ElectronicCats/RS485_Modbus_FeatherWing/Fw/Examples/ModbusRTUServerKitchenSink/ModbusRTUServerKitchenSink.ino

/*
Modbus example

  Andres Sabas @ Electronic Cats
  Original Creation Date: May 27, 2021
  Development environment specifics:

  This code is beerware; if you see me (or any other Electronic Cats
  member) at the local, and you've found our code helpful,
  please buy us a round!
  Distributed as-is; no warranty is given.
*/

#include <ArduinoRS485.h> // ArduinoModbus depends on the ArduinoRS485 library
#include <ArduinoModbus.h>

const int numCoils = 10;
const int numDiscreteInputs = 10;
const int numHoldingRegisters = 10;
const int numInputRegisters = 10;

void setup() {
  Serial.begin(9600);
  while (!Serial);

  Serial.println("Modbus RTU Server Kitchen Sink");

  // start the Modbus RTU server, with (slave) id 42
  if (!ModbusRTUServer.begin(42, 9600)) {
    Serial.println("Failed to start Modbus RTU Server!");
    while (1);
  }

  // configure coils at address 0x00
  ModbusRTUServer.configureCoils(0x00, numCoils);

  // configure discrete inputs at address 0x00
  ModbusRTUServer.configureDiscreteInputs(0x00, numDiscreteInputs);

  // configure holding registers at address 0x00
  ModbusRTUServer.configureHoldingRegisters(0x00, numHoldingRegisters);

  // configure input registers at address 0x00
  ModbusRTUServer.configureInputRegisters(0x00, numInputRegisters);
}

void loop() {
  // poll for Modbus RTU requests
  ModbusRTUServer.poll();

  // map the coil values to the discrete input values
  for (int i = 0; i < numCoils; i++) {
    int coilValue = ModbusRTUServer.coilRead(i);

    ModbusRTUServer.discreteInputWrite(i, coilValue);
  }

  // map the holding register values to the input register values
  for (int i = 0; i < numHoldingRegisters; i++) {
    long holdingRegisterValue = ModbusRTUServer.holdingRegisterRead(i);

    ModbusRTUServer.inputRegisterWrite(i, holdingRegisterValue);
  }
}
